OPRobots/IRTimer/source_code/main_module/include/icon_wifi.h

#ifndef ICON_WIFI_H
#define ICON_WIFI_H

#include <Arduino.h>

const uint16_t icon_wifi [] PROGMEM = {
	// 'irtimer_wifi_icon, 21x21px
	0x0000, 0x0000, 0x0000, 0x0000, 0x0000, 0x0000, 0x0000, 0x0000, 0x0000, 0x0000, 0x0000, 0x0000, 0x0000, 0x0000, 0x0000, 0x0000, 
	0x0000, 0x0000, 0x0000, 0x0000, 0x0000, 0x0000, 0x0000, 0x0000, 0x0000, 0x0000, 0x0000, 0x0000, 0x0000, 0x0000, 0x0000, 0x0000, 
	0x0000, 0x0000, 0x0000, 0x0000, 0x0000, 0x0000, 0x0000, 0x0000, 0x0000, 0x0000, 0x0000, 0x0000, 0x0000, 0x0000, 0x0000, 0x0000, 
	0x0000, 0x0000, 0x0000, 0x0000, 0x0000, 0x0000, 0x0000, 0x0000, 0x0000, 0x0000, 0x0000, 0x0000, 0x0000, 0x0000, 0x0000, 0x0000, 
	0x0000, 0x0000, 0x0000, 0x0000, 0x0000, 0x0000, 0x08c5, 0x2189, 0x324c, 0x326d, 0x326d, 0x29eb, 0x1127, 0x0021, 0x0000, 0x0000, 
	0x0000, 0x0000, 0x0000, 0x0000, 0x0000, 0x0000, 0x0000, 0x0000, 0x0884, 0x326d, 0x5bf5, 0x74d9, 0x7d3b, 0x857c, 0x859d, 0x859d, 
	0x855c, 0x7d1a, 0x6477, 0x4b31, 0x1989, 0x0000, 0x0000, 0x0000, 0x0000, 0x0000, 0x0000, 0x0042, 0x326d, 0x6c78, 0x857c, 0x8dbd, 
	0x8dbe, 0x8dbd, 0x859d, 0x859d, 0x859d, 0x8dbd, 0x8dbe, 0x8dbe, 0x8dbd, 0x7d1b, 0x5393, 0x1947, 0x0000, 0x0000, 0x0000, 0x1106, 
	0x53b4, 0x857c, 0x8dbe, 0x8dbd, 0x7d5b, 0x6c77, 0x5393, 0x42cf, 0x3a8e, 0x3aae, 0x4331, 0x5bf5, 0x74da, 0x859d, 0x8dbe, 0x8dbd, 
	0x74d9, 0x324d, 0x0000, 0x08a4, 0x5c16, 0x8d9d, 0x8dbd, 0x7d3b, 0x53b4, 0x21ca, 0x0022, 0x0000, 0x0000, 0x0000, 0x0000, 0x0000, 
	0x0000, 0x10e6, 0x3aaf, 0x6c98, 0x859d, 0x8dbe, 0x7d3b, 0x326d, 0x0063, 0x5393, 0x857c, 0x6c98, 0x2a0c, 0x0000, 0x0083, 0x322c, 
	0x4b72, 0x6436, 0x6c98, 0x6477, 0x5bd5, 0x42f0, 0x1968, 0x0000, 0x08e5, 0x4b72, 0x7d5c, 0x74d9, 0x29eb, 0x0000, 0x0083, 0x3aaf, 
	0x1948, 0x0000, 0x324c, 0x6457, 0x857c, 0x8dbd, 0x8dbe, 0x8dbe, 0x8dbe, 0x8dbe, 0x859d, 0x751a, 0x4b72, 0x1106, 0x0021, 0x326e, 
	0x29eb, 0x0000, 0x0000, 0x0000, 0x0000, 0x0021, 0x4311, 0x7d5b, 0x8dbe, 0x8dbd, 0x855c, 0x74d9, 0x6c98, 0x6cb8, 0x7d1b, 0x859d, 
	0x8dbe, 0x8d9d, 0x6c78, 0x1969, 0x0000, 0x0000, 0x0000, 0x0000, 0x0000, 0x0000, 0x0021, 0x4b72, 0x859d, 0x855c, 0x5bd4, 0x2a0b, 
	0x08c5, 0x0000, 0x0043, 0x1968, 0x42d0, 0x6cb9, 0x8d9d, 0x74d9, 0x21a9, 0x0000, 0x0000, 0x0000, 0x0000, 0x0000, 0x0000, 0x0000, 
	0x0083, 0x4b31, 0x3a8e, 0x0021, 0x0063, 0x21ca, 0x326d, 0x322c, 0x1127, 0x0000, 0x1127, 0x4b72, 0x29eb, 0x0000, 0x0000, 0x0000, 
	0x0000, 0x0000, 0x0000, 0x0000, 0x0000, 0x0000, 0x0000, 0x0000, 0x29eb, 0x6457, 0x7d5b, 0x859d, 0x857c, 0x74fa, 0x4b31, 0x08a4, 
	0x0000, 0x0000, 0x0000, 0x0000, 0x0000, 0x0000, 0x0000, 0x0000, 0x0000, 0x0000, 0x0000, 0x0000, 0x0000, 0x4311, 0x857c, 0x8dbe, 
	0x8dbe, 0x8dbe, 0x8dbe, 0x6cb9, 0x1147, 0x0000, 0x0000, 0x0000, 0x0000, 0x0000, 0x0000, 0x0000, 0x0000, 0x0000, 0x0000, 0x0000, 
	0x0000, 0x0000, 0x0063, 0x5393, 0x857d, 0x8dbe, 0x8dbd, 0x74d9, 0x29eb, 0x0000, 0x0000, 0x0000, 0x0000, 0x0000, 0x0000, 0x0000, 
	0x0000, 0x0000, 0x0000, 0x0000, 0x0000, 0x0000, 0x0000, 0x0000, 0x0063, 0x5393, 0x857c, 0x74d9, 0x29eb, 0x0000, 0x0000, 0x0000, 
	0x0000, 0x0000, 0x0000, 0x0000, 0x0000, 0x0000, 0x0000, 0x0000, 0x0000, 0x0000, 0x0000, 0x0000, 0x0000, 0x0000, 0x0063, 0x4311, 
	0x29eb, 0x0000, 0x0000, 0x0000, 0x0000, 0x0000, 0x0000, 0x0000, 0x0000, 0x0000, 0x0000, 0x0000, 0x0000, 0x0000, 0x0000, 0x0000, 
	0x0000, 0x0000, 0x0000, 0x0000, 0x0000, 0x0000, 0x0000, 0x0000, 0x0000, 0x0000, 0x0000, 0x0000, 0x0000, 0x0000, 0x0000, 0x0000, 
	0x0000, 0x0000, 0x0000, 0x0000, 0x0000, 0x0000, 0x0000, 0x0000, 0x0000, 0x0000, 0x0000, 0x0000, 0x0000, 0x0000, 0x0000, 0x0000, 
	0x0000, 0x0000, 0x0000, 0x0000, 0x0000, 0x0000, 0x0000, 0x0000, 0x0000, 0x0000, 0x0000, 0x0000, 0x0000, 0x0000, 0x0000, 0x0000, 
	0x0000, 0x0000, 0x0000, 0x0000, 0x0000, 0x0000, 0x0000, 0x0000, 0x0000
};

#endif
