OPRobots/IRTimer/source_code/main_module/include/rc5.h

#ifndef RC5_H
#define RC5_H


#include "config.h"
#include "control.h"
#include "stdint.h"

enum RC5_TRIGGER {
  RC5_TRIGGER_FALLING,
  RC5_TRIGGER_RISING,
};

#define RC5_DATA_LENGTH 2

void rc5_init(void);
void rc5_register(enum RC5_TRIGGER trigger);
void rc5_isr(void);
void rc5_update(void);

#endif
